otoivanen/esp8266-tehowatti/case/Relay.SLDPRT

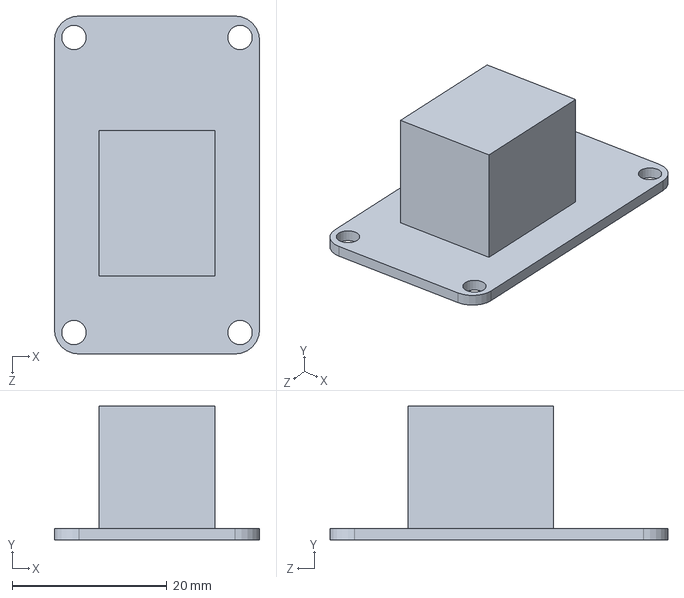
[picture p19: CAD file, 2025-01-11]
case/Relay.SLDPRT
26.5 x 17.3 x 43.7 mm
