otoivanen/esp8266-tehowatti/case/STL/Lid.STL

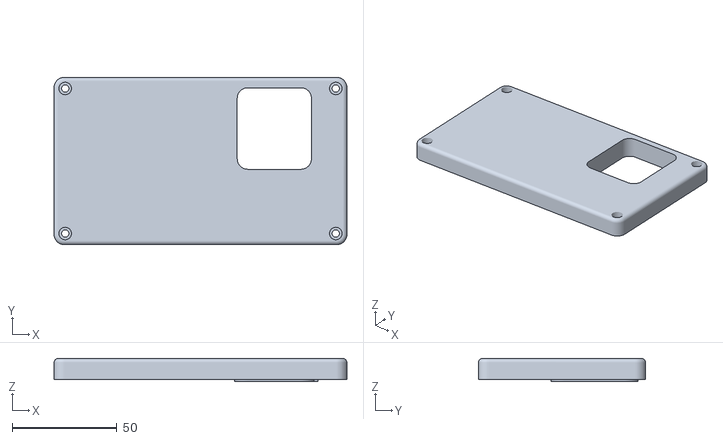
[picture p20: CAD file, 2025-01-11]
case/STL/Lid.STL
140.0 x 80.0 x 11.0
