otoivanen/esp8266-tehowatti/case/Body1.SLDPRT

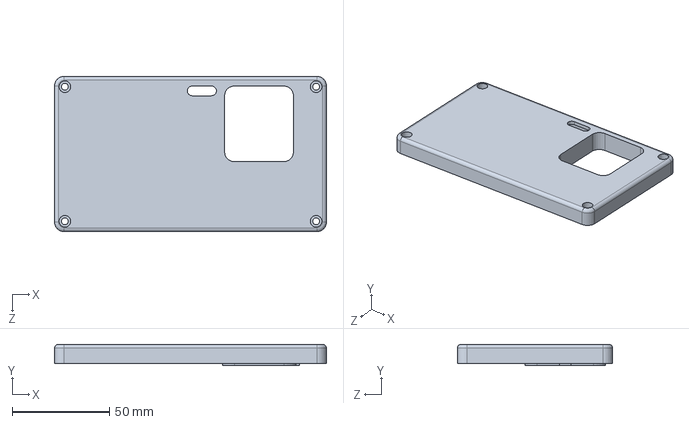
[picture p21: CAD file, 2025-01-11]
case/Body1.SLDPRT
140.0 x 11.0 x 80.0 mm
