otoivanen/esp8266-tehowatti/case/Cable gland.SLDPRT

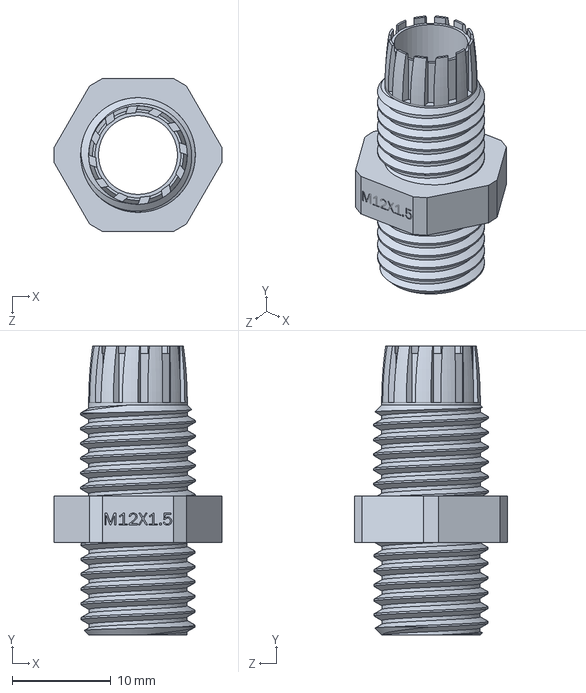
[picture p22: CAD file, 2025-01-11]
case/Cable gland.SLDPRT
17.0 x 29.3 x 15.5 mm
