otoivanen/esp8266-tehowatti/case/Wago serie 221.SLDPRT

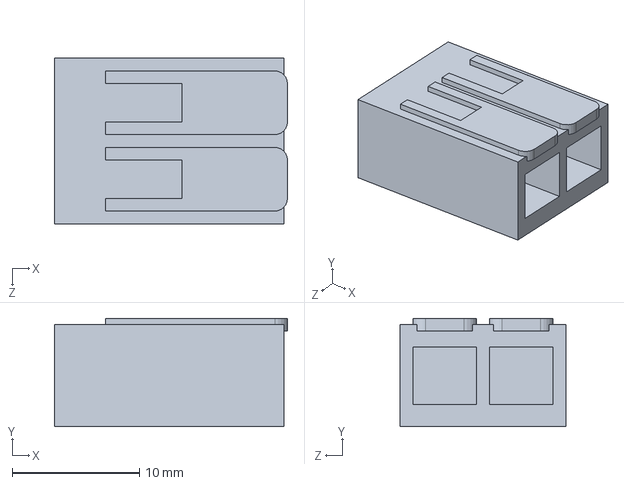
[picture p23: CAD file, 2025-01-11]
case/Wago serie 221.SLDPRT
18.3 x 8.50 x 13.0 mm
